foxBMS/foxBMS-primary/src/module/config/contactor_cfg.h

/**
 *
 * @copyright &copy; 2010 - 2017, Fraunhofer-Gesellschaft zur Foerderung der angewandten Forschung e.V. All rights reserved.
 *
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
 * THIS SOFTWARE IS PROVIDED BY THE COPYRIGHT HOLDERS AND CONTRIBUTORS "AS IS" AND ANY EXPRESS OR IMPLIED WARRANTIES, INCLUDING, BUT NOT LIMITED TO, THE IMPLIED WARRANTIES OF MERCHANTABILITY AND FITNESS FOR A PARTICULAR PURPOSE ARE DISCLAIMED. IN NO EVENT SHALL THE COPYRIGHT HOLDER OR CONTRIBUTORS BE LIABLE FOR ANY DIRECT, INDIRECT, INCIDENTAL, SPECIAL, EXEMPLARY, OR CONSEQUENTIAL DAMAGES (INCLUDING, BUT NOT LIMITED TO, PROCUREMENT OF SUBSTITUTE GOODS OR SERVICES; LOSS OF USE, DATA, OR PROFITS; OR BUSINESS INTERRUPTION) HOWEVER CAUSED AND ON ANY THEORY OF LIABILITY, WHETHER IN CONTRACT, STRICT LIABILITY, OR TORT (INCLUDING NEGLIGENCE OR OTHERWISE) ARISING IN ANY WAY OUT OF THE USE OF THIS SOFTWARE, EVEN IF ADVISED OF THE POSSIBILITY OF SUCH DAMAGE.
 *
 * We kindly request you to use one or more of the following phrases to refer to foxBMS in your hardware, software, documentation or advertising materials:
 *
 * &Prime;This product uses parts of foxBMS&reg;&Prime;
 *
 * &Prime;This product includes parts of foxBMS&reg;&Prime;
 *
 * &Prime;This product is derived from foxBMS&reg;&Prime;
 *
 */

/**
 * @file    contactor_cfg.h
 * @author  foxBMS Team
 * @date    23.09.2015 (date of creation)
 * @ingroup DRIVERS_CONF
 * @prefix  CONT
 *
 * @brief   Header for the configuration for the driver for the contactors
 *
 * This file defines all needed macros to map the interlock and the contactors'
 * hardware configuration to the software.
 *
 */

#ifndef CONTACTOR_CFG_H_
#define CONTACTOR_CFG_H_

/*================== Includes =============================================*/
#include "batterysystem_cfg.h"
#include "io_cfg.h"


/*================== Macros and Definitions ===============================*/

/**
 * Use this define as virtual feedback "pin" if a contactor has no
 * feedback pin
 */
#define CONT_HAS_NO_FEEDBACK ((IO_PORTS_e)(0xFF))

/*fox
 * defines the number of  trigger calls, after the state of a
 * contactor with no feedback pin is assumed to be in its requested state.
 *
 * @var     trigger counter for contactor state
 * @type    int
 * @default 100
 * @valid   [90,110]
 * @units   ms
 * @level   advanced
 * @group   CONTACTOR
 */
/**
 * defines the number of  trigger calls, after the state of a
 * contactor with no feedback pin is assumed to be in its requested state.
 */
#define CONT_HAS_NO_FEEDBACK_SWICHTING_TIME 100

/*fox
 * defines the maximum time after the requested state has to be the
 * current state of a contactor
 * @var     maximum time between allowed between switch order to contactor and effective switch
 * @type    int
 * @default 100
 * @valid   [90,110]
 * @units   ms
 * @level   advanced
 * @group   CONTACTOR
 */
/**
 * defines the maximum time after the requested state has to be the
 *  current state of a contactor
 */
#define CONT_MAXIUMUM_ALLOWED_CONTACTOR_SWITCHING_TIME 100

/*fox
 * defines the number of bad countings of opening contactors at too
 *  high current
 * @var     counter for bad contactor opening
 * @type    int
 * @default 10
 * @valid   [9,11]
 * @level   advanced
 * @group   CONTACTOR
 */
/**
 * defines the number of bad countings of opening contactors at too
 * high current
 */
#define CONT_NUMBER_OF_BAD_COUNTINGS 10

/*fox
 * This macro describes the limiting current from the the positive to
 * negative side of the contactor at which a damaging of the
 * contactor occurs. If this limit is the exceeded the contacor
 * module makes an entry in the diagnosis module indicating a
 * switching off of the contactors under a bad  condition.
 *
 * @var     bad switch off current pos
 * @type    float
 * @default 1.0
 * @valid   [1000.0,2000.0]
 * @level   advanced
 * @unit    mA
 * @group   CONTACTOR
 */
/**
 * This macro describes the limiting current from the the positive to
 * negative side of the contactor at which a damaging of the
 * contactor occurs. If this limit is the exceeded the contacor
 * module makes an entry in the diagnosis module indicating a
 * switching off of the contactors under a bad  condition.
 */
#define BAD_SWITCHOFF_CURRENT_POS 1000.0

/*fox
 * This macro describes the limiting current from the the negative to
 * positive side of the contactor at which a damaging of the
 * contactor occurs. If this limit is the exceeded the contacor
 * module makes an entry in the diagnosis module indicating a
 * switching off of the contactors under a bad  condition.
 *
 * @var     bad switch off current neg
 * @type    float
 * @default -1.0
 * @valid   [-2000.0,-1000.0]
 * @level   advanced
 * @unit    mA
 * @group   CONTACTOR
 */
/**
 * This macro describes the limiting current from the the negative to
 * positive side of the contactor at which a damaging of the
 * contactor occurs. If this limit is the exceeded the contacor
 * module makes an entry in the diagnosis module indicating a
 * switching off of the contactors under a bad  condition.
 */
#define BAD_SWITCHOFF_CURRENT_NEG -1000.0

/*fox
 * if CONT_IGNORE_INIT_CHECK is defined CONT_Init() always returns
 * E_OK.
 * This is for pure HW-master debugging and must not be activated
 * in any other situation.
 * @var     ignore contactor check
 * @type    toggle
 * @default False
 * @level   debug
 * @group   CONTACTOR
 */
//#define CONT_IGNORE_CONT_INIT_CHECK


/*
 * The number of defines per contactor must be the same as the length
 *  of the array cont_contactors_cfg in contactor_cfg.c
 * Every contactor consists of 1 control pin and 1 feedback pin
 * counting together as 1 contactor.
 * E.g. if you have 1 contactor your define has to be:
 *      #define CONT_INTERLOCK_CONTROL       IO_PIN_MCU_0_INTERLOCK_CONTROL
 *      #define CONT_INTERLOCK_FEEDBACK      IO_PIN_MCU_0_INTERLOCK_FEEDBACK
 */
#define CONT_INTERLOCK_CONTROL                  IO_PIN_MCU_0_INTERLOCK_CONTROL
#define CONT_INTERLOCK_FEEDBACK                 IO_PIN_MCU_0_INTERLOCK_FEEDBACK

#define CONT_PLUS_MAIN_CONTROL                  IO_PIN_MCU_0_CONTACTOR_0_CONTROL
#define CONT_PLUS_MAIN_FEEDBACK                 IO_PIN_MCU_0_CONTACTOR_0_FEEDBACK

#define CONT_PLUS_PRECHARGE_CONTROL             IO_PIN_MCU_0_CONTACTOR_1_CONTROL
#define CONT_PLUS_PRECHARGE_FEEDBACK            IO_PIN_MCU_0_CONTACTOR_1_FEEDBACK

#define CONT_MINUS_MAIN_CONTROL                 IO_PIN_MCU_0_CONTACTOR_2_CONTROL
#define CONT_MINUS_MAIN_FEEDBACK                IO_PIN_MCU_0_CONTACTOR_2_FEEDBACK

#if BS_SEPARATE_POWERLINES == 1
#define CONT_CHARGE_PLUS_MAIN_CONTROL           IO_PIN_MCU_0_CONTACTOR_3_CONTROL
#define CONT_CHARGE_PLUS_MAIN_FEEDBACK          IO_PIN_MCU_0_CONTACTOR_3_FEEDBACK

#define CONT_CHARGE_PLUS_PRECHARGE_CONTROL      IO_PIN_MCU_0_CONTACTOR_4_CONTROL
#define CONT_CHARGE_PLUS_PRECHARGE_FEEDBACK     IO_PIN_MCU_0_CONTACTOR_4_FEEDBACK

#define CONT_CHARGE_MINUS_MAIN_CONTROL          IO_PIN_MCU_0_CONTACTOR_5_CONTROL
#define CONT_CHARGE_MINUS_MAIN_FEEDBACK         IO_PIN_MCU_0_CONTACTOR_5_FEEDBACK
#endif // BS_SEPARATE_POWERLINES == 1
/*
 * additional possible contactors from the io definition
#define CONT_X3_CONTROL                         IO_PIN_MCU_0_CONTACTOR_6_CONTROL
#define CONT_X3_FEEDBACK                        IO_PIN_MCU_0_CONTACTOR_6_FEEDBACK

#define CONT_X4_CONTROL                         IO_PIN_MCU_0_CONTACTOR_7_CONTROL
#define CONT_X4_FEEDBACK                        IO_PIN_MCU_0_CONTACTOR_7_FEEDBACK

#define CONT_X5_CONTROL                         IO_PIN_MCU_0_CONTACTOR_8_CONTROL
#define CONT_X5_FEEDBACK                        IO_PIN_MCU_0_CONTACTOR_8_FEEDBACK

*/


/*================== Constant and Variable Definitions ====================*/
/**
 * Symbolic names for contactors' possible states
 */
typedef enum {
    CONT_SWITCH_OFF     = 0,    /*!< Contactor off         --> Contactor is open           */
    CONT_SWITCH_ON      = 1,    /*!< Contactor on          --> Contactor is closed         */
    CONT_SWITCH_UNDEF   = 2,    /*!< Contactor undefined   --> Contactor state not known   */
} CONT_SWITCH_e;

/**
 * Symbolic names for the contactors, which are used in 
 * the contactor_cfg[] array
 */
typedef enum {
    CONT_PLUS_MAIN              = 0,    /*!< Main contactor in the positive path of the powerline      */
    CONT_PLUS_PRECHARGE         = 1,    /*!< Precharge contactor in the positive path of the powerline */
    CONT_MINUS_MAIN             = 2,    /*!< Main contactor in the negative path of the powerline      */
    CONT_CHARGE_PLUS_MAIN       = 3,    /*!< Main contactor in the positive charge path of the powerline      */
    CONT_CHARGE_PLUS_PRECHARGE  = 4,    /*!< Precharge contactor in the positive charge path of the powerline */
    CONT_CHARGE_MINUS_MAIN      = 5,    /*!< Main contactor in the negative charge path of the powerline      */
} CONT_NAMES_e;

/**
 * Symbolic names defining the electric behavior of the contactor
 */
typedef enum {
    CONT_FEEDBACK_NORMALLY_OPEN     = 0,    /*!< Feedback line of a contactor is normally open      */
    CONT_FEEDBACK_NORMALLY_CLOSED   = 1,    /*!< Feedback line of a contactor is normally closed    */
    CONT_FEEDBACK_TYPE_DONT_CARE    = 0xFF  /*!< Feedback line of the contactor is not used         */
} CONT_FEEDBACK_ELECTRICAL_CONTACT_e;

/**
 * typedef to store the time stamp when a contactor was set to a certain set value.
 * This is later used in typedef CONT_STATES_s.
 */
typedef struct {
    boolean setvalue;
    uint32_t timestamp;
} CONT_STATE_SET_s;

/**
 * typedef to store the time stamp when a contactor state was set to the expected value based on the request.
 * This is later used in typedef CONT_STATES_s.
 */
typedef struct {
    CONT_SWITCH_e feedback;
    uint32_t timestamp;
} CONT_STATE_EXPECTATION_s;

/**
 * typedef to store the time stamp of the last time the feedback line of the contactor was measured.
 * This is later used in typedef CONT_STATES_s.
 */
typedef struct {
    CONT_SWITCH_e feedback;
    uint32_t timestamp;
} CONT_STATE_MEASUREMENT_s;

/**
 * struct to sum up all contactor conditions (setvalue, expectation and measurement)
 */
typedef struct {
    CONT_STATE_SET_s set;
    CONT_STATE_EXPECTATION_s expectation;
    CONT_STATE_MEASUREMENT_s measurement;
} CONT_STATES_s;

/**
 * Represents the hardware configuration of the contactor
 */
typedef struct {
    IO_PORTS_e control_pin;
    IO_PORTS_e feedback_pin;
    CONT_FEEDBACK_ELECTRICAL_CONTACT_e feedback_pin_electrical_contact;
} CONT_CFG_s;

extern CONT_CFG_s cont_interlock_cfg;
extern CONT_STATES_s cont_interlock_state;
extern CONT_CFG_s cont_contactors_cfg [BS_NR_OF_CONTACTORS];
extern CONT_STATES_s cont_contactor_states[BS_NR_OF_CONTACTORS];

extern const uint8_t cont_contactors_cfg_length;
extern const uint8_t cont_contactors_states_length;

/*================== Function Prototypes ==================================*/

/*================== Function Implementations =============================*/

#endif /* CONTACTOR_CFG_H_ */
