foxBMS/foxBMS-primary/src/general/nvic.c

/**
 *
 * @copyright &copy; 2010 - 2017, Fraunhofer-Gesellschaft zur Foerderung der angewandten Forschung e.V. All rights reserved.
 *
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
 * THIS SOFTWARE IS PROVIDED BY THE COPYRIGHT HOLDERS AND CONTRIBUTORS "AS IS" AND ANY EXPRESS OR IMPLIED WARRANTIES, INCLUDING, BUT NOT LIMITED TO, THE IMPLIED WARRANTIES OF MERCHANTABILITY AND FITNESS FOR A PARTICULAR PURPOSE ARE DISCLAIMED. IN NO EVENT SHALL THE COPYRIGHT HOLDER OR CONTRIBUTORS BE LIABLE FOR ANY DIRECT, INDIRECT, INCIDENTAL, SPECIAL, EXEMPLARY, OR CONSEQUENTIAL DAMAGES (INCLUDING, BUT NOT LIMITED TO, PROCUREMENT OF SUBSTITUTE GOODS OR SERVICES; LOSS OF USE, DATA, OR PROFITS; OR BUSINESS INTERRUPTION) HOWEVER CAUSED AND ON ANY THEORY OF LIABILITY, WHETHER IN CONTRACT, STRICT LIABILITY, OR TORT (INCLUDING NEGLIGENCE OR OTHERWISE) ARISING IN ANY WAY OUT OF THE USE OF THIS SOFTWARE, EVEN IF ADVISED OF THE POSSIBILITY OF SUCH DAMAGE.
 *
 * We kindly request you to use one or more of the following phrases to refer to foxBMS in your hardware, software, documentation or advertising materials:
 *
 * &Prime;This product uses parts of foxBMS&reg;&Prime;
 *
 * &Prime;This product includes parts of foxBMS&reg;&Prime;
 *
 * &Prime;This product is derived from foxBMS&reg;&Prime;
 *
 */

/**
 * @file    nvic.c
 * @author  foxBMS Team
 * @date    10.09.2015 (date of creation)
 * @ingroup GENERAL
 * @prefix  NVIC
 *
 * @brief   Functions for setting and enabling interrupts
 *
 * The MCU has 16 interrupt priority levels:
 * Priority number 0 means highest (strongest) priority
 * Priority number 15 means lowest (weakest) priority
 *
 * FreeRTOS priority model:
 * The systick interrupt has the lowest priority
 * FreeRTOSConfig.h defines the max syscall priority in configLIBRARY_MAX_SYSCALL_INTERRUPT_PRIORITY
 * Interrupts which uses FreeRTOS syscalls have to be assigned to a priority number >= max syscall priority
 * (priority is not stronger than max syscall priority), however they can only use syscalls like xxx_fromISR().
 * Real-Time-Interrupts should be configured to a priority number < max syscall priority, thus they could not be blocked by FreeRTOS
 * because the blocking priority level is configLIBRARY_MAX_SYSCALL_INTERRUPT_PRIORITY.
 * Real-Time-Interrupts must not use FreeRTOS-API like xxx_fromISR().
 *
 * All task priorities are weaker than the interrupt priorities, the strongest task priority will be interrupted by the weakest
 * interrupt priority.
 *
 * Example: max syscall priority = 5
 *
 *     Priority number        description
 * |    Task priorities       Always weaker than interrupts
 * |    15                    Systick interrupt, weakest interrupt
 * |    14..5                 Interrupts which use FreeRTOS syscalls
 * |    4..1                  Real-Time Interrupts
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
